daveho/carpi/CarPi/file_navigator_menu_controller.h

// CarPi - Raspberry Pi car entertainment system
// Copyright (c) 2013,2014 David H. Hovemeyer <david.hovemeyer@gmail.com>

// This file is part of CarPi.
// 
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
#ifndef FILENAVIGATORMENUCONTROLLER_H
#define FILENAVIGATORMENUCONTROLLER_H

#include <string>
#include <vector>
#include "menu_controller.h"

//
// MenuController specialization for file navigation.
//
class FileNavigatorMenuController : public MenuController
{
private:
	std::vector<std::string> m_dirStack;
	std::vector<size_t> m_selectedItemStack;
	
	typedef MenuController Base;
	
public:
	// Menu item value constants.
	enum {
		// menu item value for parent directory: "special" items should have lower values
		PARENT_DIR_VALUE = 98,
		
		// menu item value for special menu item created
		// when a directory cannot be read
		INVALID_DIR_VALUE = 99,
		
		// menu item value for first actual file or subdirectory
		FIRST_FILE_VALUE = 100,
	};

	FileNavigatorMenuController(const std::string &baseDir);
	~FileNavigatorMenuController();
	
	// Get current directory.
	const std::string &getCurrentDir() const { return m_dirStack.back(); }
	
	virtual void visitButtonEvent(ButtonEvent *evt);
	virtual void visitNotificationEvent(NotificationEvent *evt);
	
	// Downcall method: subclasses can override to filter files and directories.
	// Default is that all entries are included.
	virtual bool includeEntry(const std::string &entryName, int flags);
	
	// Downcall method: called when menu items are populated,
	// subclass can override to add/remove items.
	// Default implementation is a no-op.
	virtual void onMenuPopulated(Menu *menu);

protected:
	static std::string getFullPath(const std::string &dirName, const std::string &entryName);
	
private:
	void populateMenuItems();
	void onDirectoryChanged(size_t selectedItem);
};

#endif // FILENAVIGATORMENUCONTROLLER_H
