daveho/carpi/CarPi/console.cpp

// CarPi - Raspberry Pi car entertainment system
// Copyright (c) 2013, David H. Hovemeyer <david.hovemeyer@gmail.com>

// This file is part of CarPi.
// 
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
#include <cassert>
#include <cstdarg>
#include <ncurses.h>
#include "console.h"

namespace {
	Console *s_instance;
}

Console::Console()
	: m_numRows(-1)
	, m_numCols(-1)
	, m_attr(0)
{
}

Console::~Console()
{
}

void Console::initialize()
{
	assert(s_instance == 0);
	s_instance = new Console();
}

Console *Console::instance()
{
	assert(s_instance != 0);
	return s_instance;
}

void Console::init()
{
	initscr();
	cbreak();
	noecho();
	nonl();
	
	getmaxyx(stdscr, m_numRows, m_numCols);

	start_color();
	
	// Initialize color pairs for the 64 "standard" color combinations.
	for (int i = 0; i < 64; i++) {
		init_pair(i+1, i&0x7, (i>>3)&0x7);
	}
}

void Console::cleanup()
{
	nl();
	echo();
	nocbreak();
	endwin();
}

int Console::getNumRows()
{
	return m_numRows;
}

int Console::getNumCols()
{
	return m_numCols;
}

void Console::clear()
{
	erase();
}

void Console::clearToEOL()
{
	clrtoeol();
}

void Console::moveCursor(int row, int col)
{
	move(row, col);
}

void Console::attr(int bg, int fg)
{
	m_attr = ((bg&0xF) << 4) | (fg&0xF);
}

void Console::print(const std::string &s)
{
	setAttrs();
	printw("%s", s.c_str());
}

void Console::printf(const char *fmt, ...)
{
	setAttrs();
	
	va_list args;
	va_start(args, fmt);
	vwprintw(stdscr, fmt, args);
	va_end(args);
}

void Console::printCenter(int row, const std::string &s)
{
	if (int(s.size()) > m_numCols) {
		moveCursor(row, 0);
		print(s.substr(0, m_numCols));
	} else {
		int excess = m_numCols - int(s.size());
		moveCursor(row, 0);
		clearToEOL();
		moveCursor(row, excess/2);
		print(s);
	}
}

void Console::commit()
{
	refresh();
}

void Console::setAttrs()
{
	int bg = (m_attr>>4)&0xF;
	int fg = (m_attr&0xF);

	// Enable the color pair containing the "standard" color
	// (ignoring the INTENSE component).
	int pair = (((bg&7) << 3) | (fg&7)) + 1;
	attron(COLOR_PAIR(pair));

	// INTENSE foreground means A_BOLD.
	if ((fg & 8) != 0) {
		attron(A_BOLD);
	} else {
		attroff(A_BOLD);
	}
	
	// INTENSE background means A_BLINK.
	// Most terminal emulators interpret this as intense background
	// rather than actual blinking.
	if ((bg & 8) != 0) {
		attron(A_BLINK);
	} else {
		attroff(A_BLINK);
	}
}
