daveho/carpi/CarPi/string_util.h

// CarPi - Raspberry Pi car entertainment system
// Copyright (c) 2013-2017 David H. Hovemeyer <david.hovemeyer@gmail.com>

// This file is part of CarPi.
// 
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
#ifndef STRING_UTIL_H
#define STRING_UTIL_H

#include <cstdio>
#include <cctype>
#include <string>
#include <vector>
#include <algorithm>

namespace StringUtil {
	inline bool endsWith(const std::string &s, const std::string &suffix)
	{
		// See: http://stackoverflow.com/questions/874134/find-if-string-endswith-another-string-in-c
		if (s.size() < suffix.size()) { return false; }
		return std::mismatch(suffix.rbegin(), suffix.rend(), s.rbegin()).first == suffix.rend();
	}
	
	inline bool startsWith(const std::string &s, const std::string &prefix)
	{
		// Same idea as endsWith
		if (s.size() < prefix.size()) { return false; }
		return std::mismatch(prefix.begin(), prefix.end(), s.begin()).first == prefix.end();
	}
	
	inline std::string trimToSize(const std::string &s, size_t n)
	{
		return (s.size() <= n) ? s : s.substr(0, n);
	}
	
	inline std::string padWithSpaces(const std::string &s, size_t n)
	{
		std::string result(s);
		if (result.size() > n) {
			result = trimToSize(s, n);
		}
		while (result.size() < n) {
			result += ' ';
		}
		return result;
	}
	
	// Trim leading and trailing space characters from given string
	inline std::string trimSpaces(const std::string &s)
	{
		if (s.empty()) { return s; }
		
		// Skip leading space characters
		size_t n = 0;
		while (n < s.size() && isspace(s[n])) {
			n++;
		}
		
		// Skip trailing space characters
		size_t e = s.size();
		while (e > n && isspace(s[e-1])) {
			e--;
		}
		
		return s.substr(n, s.size() - (n+(s.size()-e)));
	}
	
	// Source:
	//   http://stackoverflow.com/questions/10051679/c-tokenize-string
	// I changed the function name and indentation style, but otherwise
	// it's copied verbatim.
	inline std::vector<std::string> tokenize(const std::string &source, const char *delimiter = " ", bool keepEmpty = false)
	{
		std::vector<std::string> results;

		size_t prev = 0;
		size_t next = 0;

		while ((next = source.find_first_of(delimiter, prev)) != std::string::npos) {
			if (keepEmpty || (next - prev != 0)) {
				results.push_back(source.substr(prev, next - prev));
			}
			prev = next + 1;
		}

		if (prev < source.size()) {
			results.push_back(source.substr(prev));
		}

		return results;
	}

	// Read a line of text from given file handle.
	// Result is assigned to the string parameter.
	// Returns false if EOF is reached without reading
	// any characters.  There is some complicated code here
	// to account for the fact that omxplayer uses CR
	// rather than NL to terminate lines.  (Ugh.)
	inline bool readLine(FILE *f, std::string &line)
	{
		line.clear();
		bool sawCR = false;
		for (;;) {
			int c = fgetc(f);
			if (c == EOF) {
				// End of file: we have a line if we read anything
				return !line.empty() || sawCR;
			}
			if (c == '\n') {
				// Line terminated by a good old NL character
				break;
			}
			if (c == '\r') {
				if (sawCR) {
					// Two CRs in a row: treat the first as terminating the line (and put back the second)
					ungetc(c, f);
					break;
				} else {
					// Saw initial CR character: make a note, but don't add it to the string
					sawCR = true;
				}
			} else {
				if (sawCR) {
					// Saw a CR followed by a non-CR character: treat the CR as a line terminator
					// (and put back the non-CR character since it's part of the next line)
					ungetc(c, f);
					break;
				} else {
					// Not a line terminator, so add it to the result string
					line += char(c);
				}
			}
		}
		return true;
	}

	// Read one line of text from named file
	inline bool readOneLine(const std::string &fileName, std::string &line)
	{
		FILE *fh = fopen(fileName.c_str(), "r");
		if (!fh) {
			return false;
		}
		bool gotLine = readLine(fh, line);
		fclose(fh);
		return gotLine;
	}

	// Return just the file part of a path
	inline std::string getFilePart(const std::string &path)
	{
		size_t pos = path.find_last_of('/');
		if (pos == std::string::npos) {
			return path;
		} else {
			return path.substr(pos+1, path.size());
		}
	}
};

#endif // STRING_UTIL_H
